surgtechlab/MagSense/boardV2Ideas/kl02.png

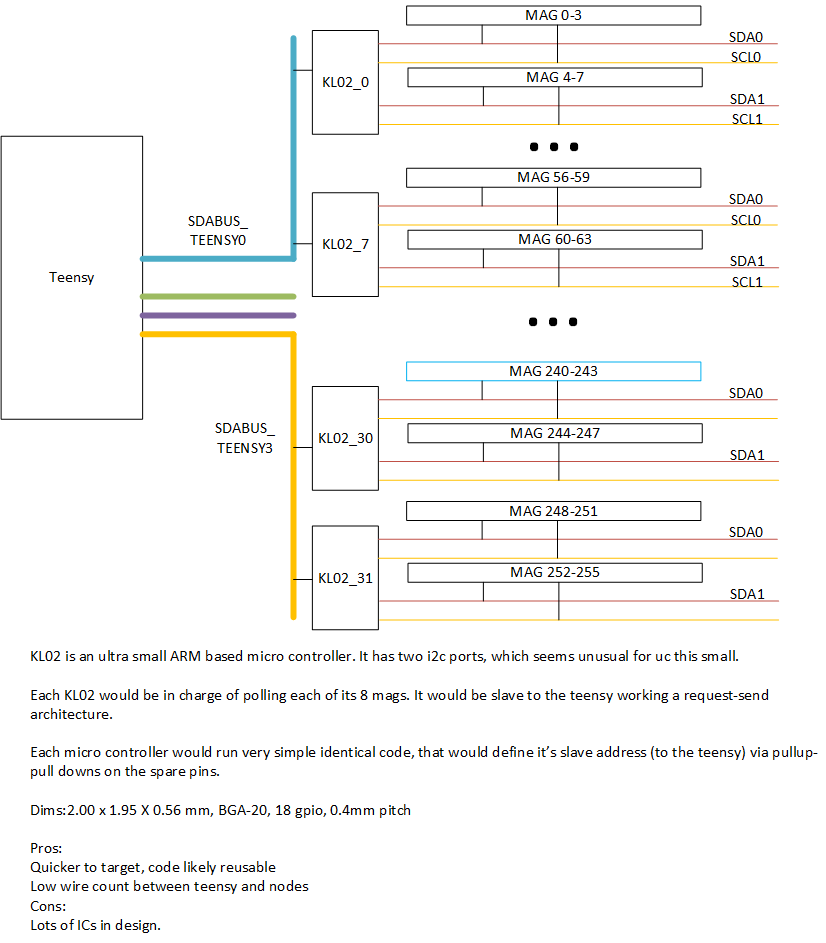
boardV2Ideas/kl02.png
