surgtechlab/MagSense/boardV2Ideas/kl02_spi.png

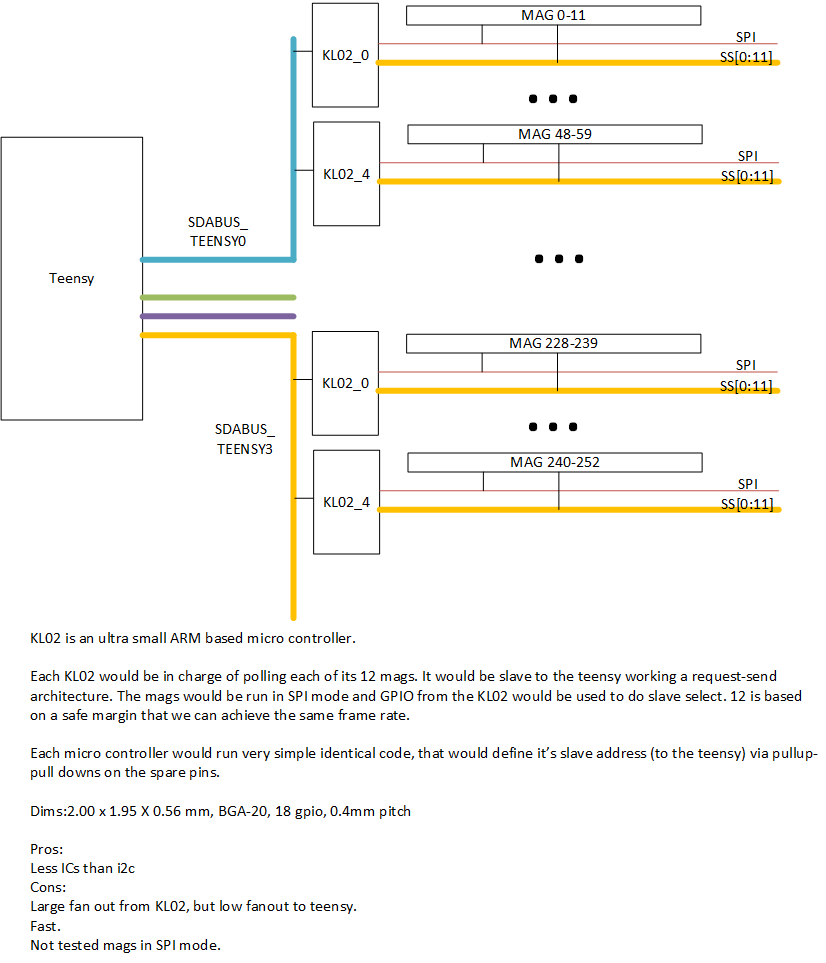
boardV2Ideas/kl02_spi.png
