surgtechlab/MagSense/boardV2Ideas/shiftMSB.png

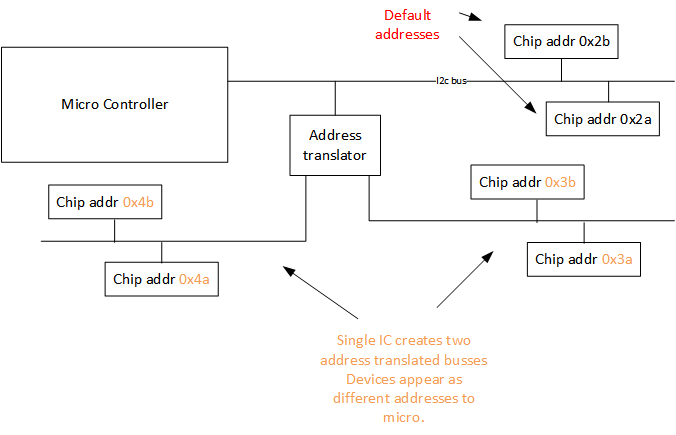
boardV2Ideas/shiftMSB.png
