surgtechlab/MagSense/boardV2Ideas/unifiedArchitechture.png

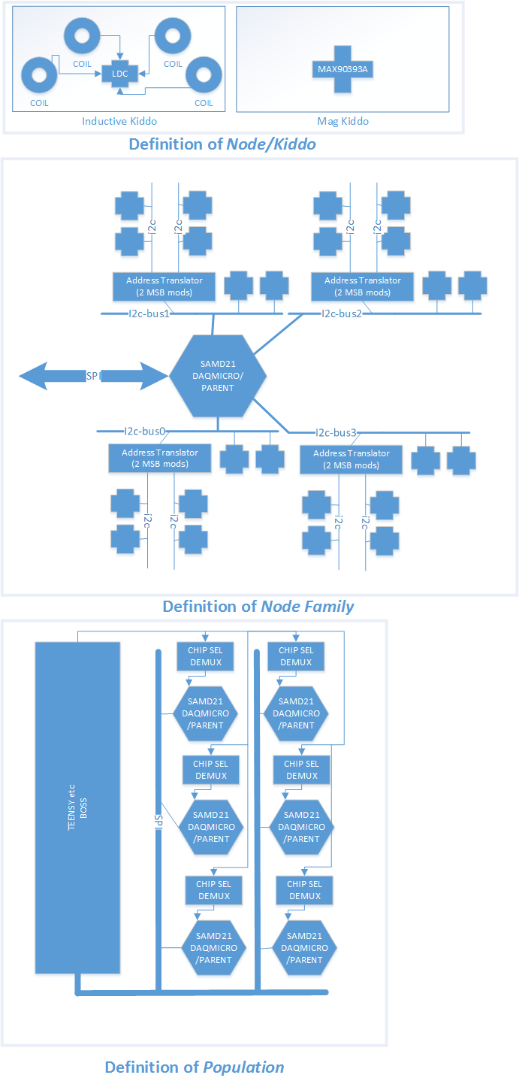
boardV2Ideas/unifiedArchitechture.png
