surgtechlab/MagSense/FootPlate_LabVIEW_Client/Recorded_Data/ESCAPES_004/ESCAPES 004 Trial Notes.jpg

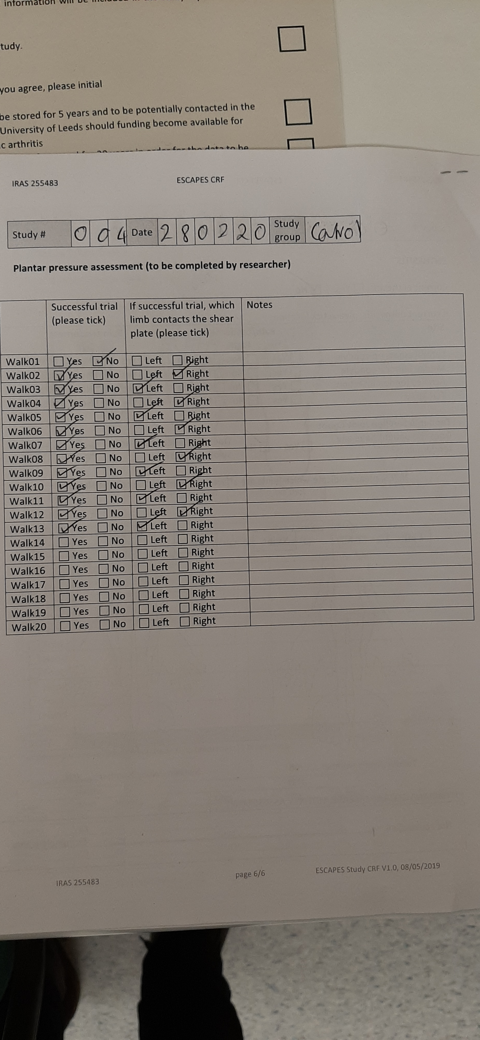
FootPlate_LabVIEW_Client/Recorded_Data/ESCAPES_004/ESCAPES 004 Trial Notes.jpg
