surgtechlab/MagSense/FootPlate_LabVIEW_Client/Recorded_Data/ESCAPES_005/ESCAPES 005 Trial Notes.jpg

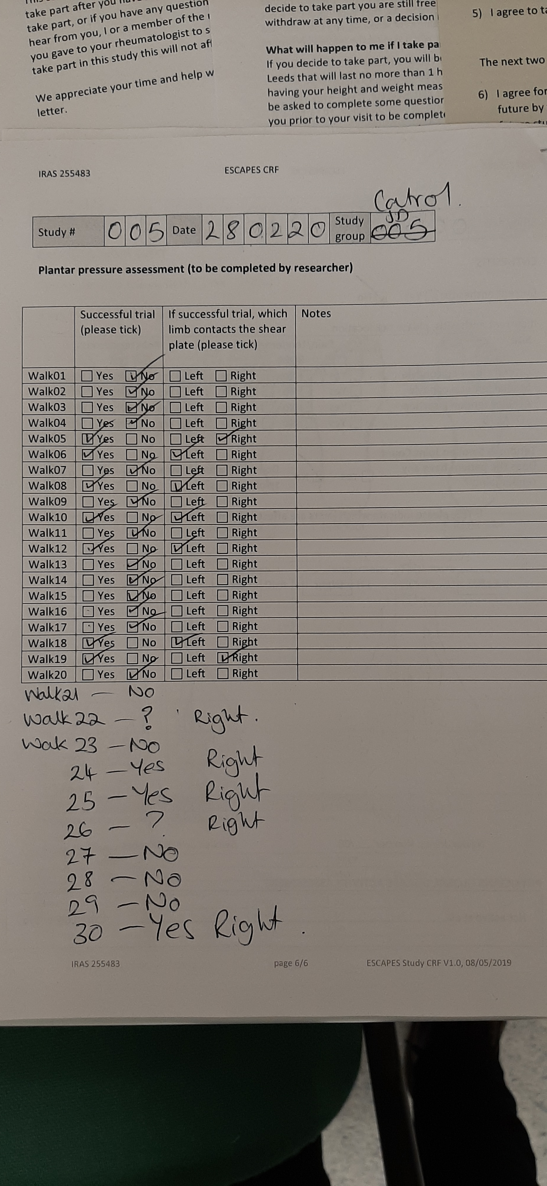
FootPlate_LabVIEW_Client/Recorded_Data/ESCAPES_005/ESCAPES 005 Trial Notes.jpg
