surgtechlab/MagSense/FootPlate_LabVIEW_Client/Recorded_Data/ESCAPES_006/ESCAPES 006 Trial Notes.jpg

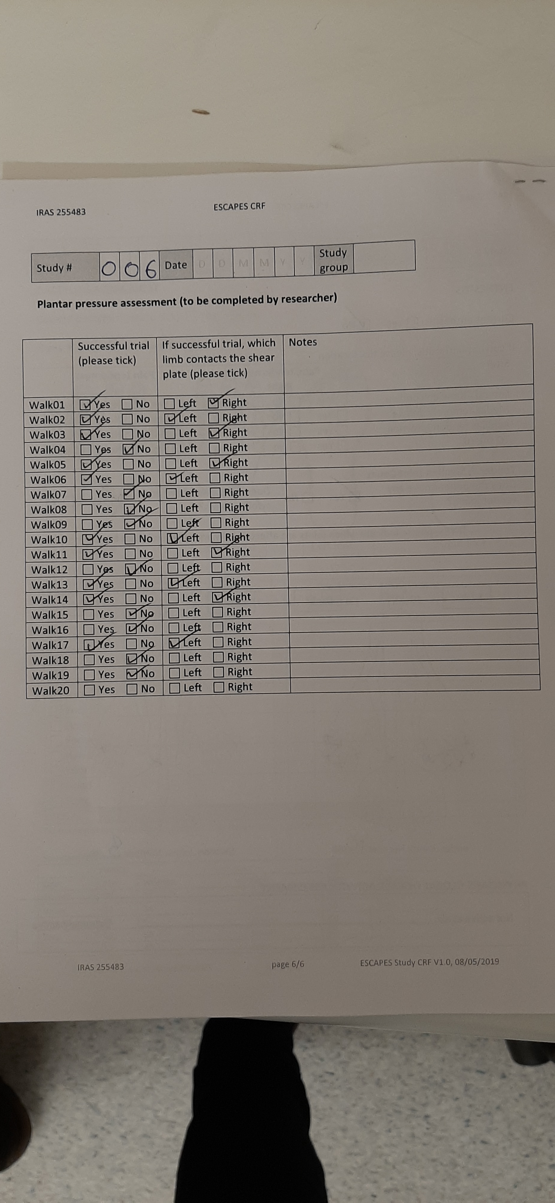
FootPlate_LabVIEW_Client/Recorded_Data/ESCAPES_006/ESCAPES 006 Trial Notes.jpg
